umbertoragone/nanoupdi/images/nanoupdi_8.jpg

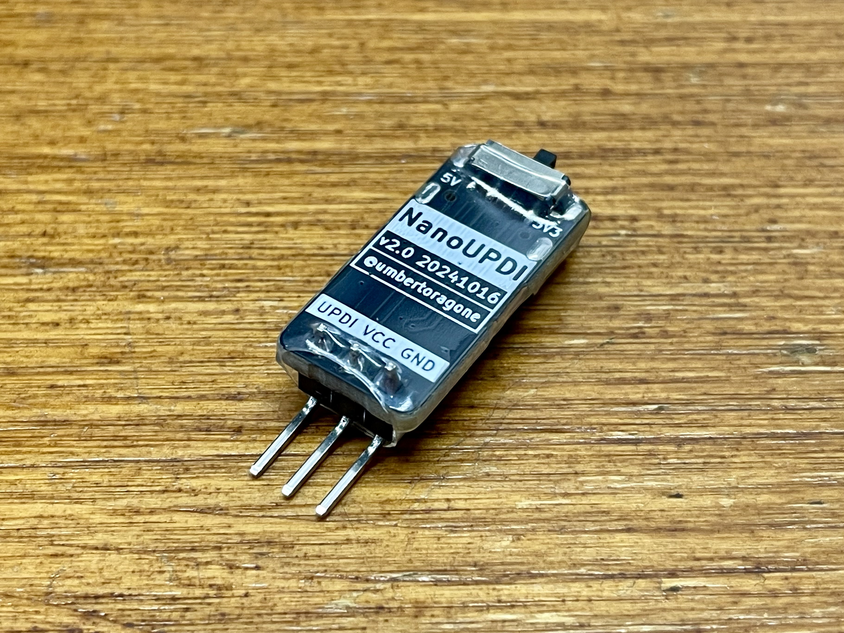
images/nanoupdi_8.jpg
