umbertoragone/nanoupdi/renders/NanoUPDI_programmer_v2_front.jpg

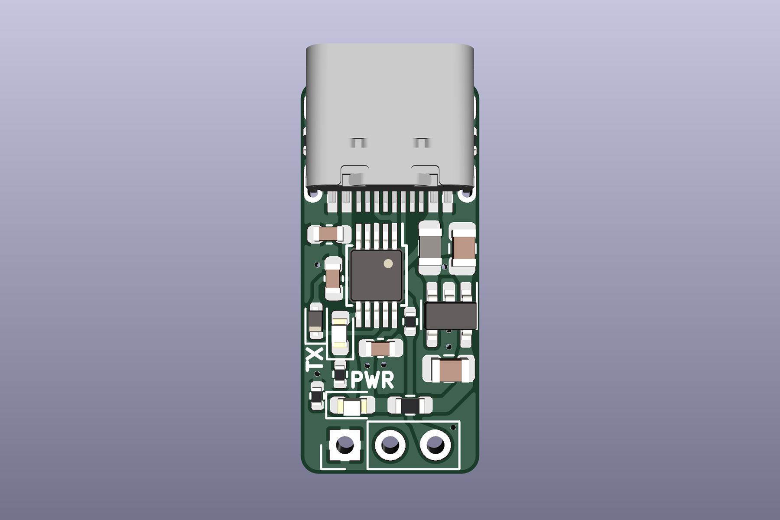
renders/NanoUPDI_programmer_v2_front.jpg
