umbertoragone/nanoupdi/bom/ibom_preview_back.png

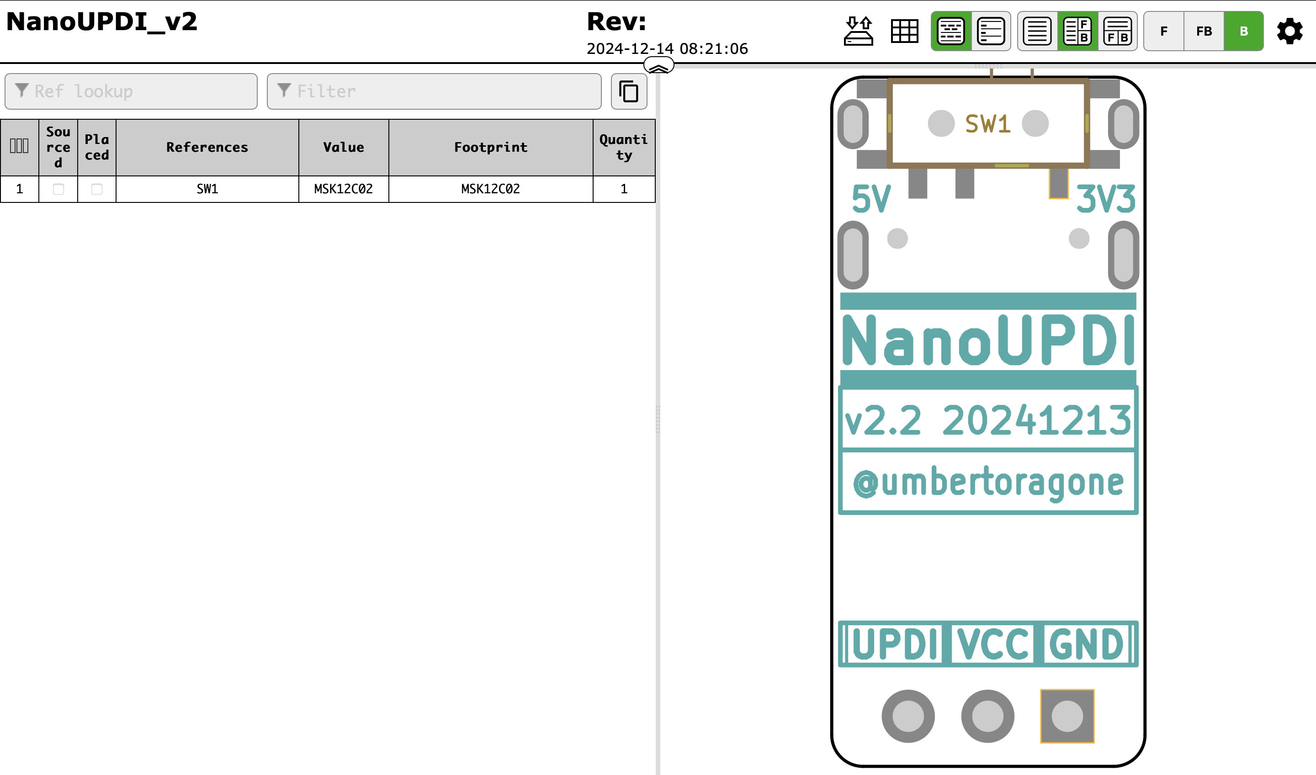
bom/ibom_preview_back.png
