umbertoragone/nanoupdi/bom/ibom_preview_front.png

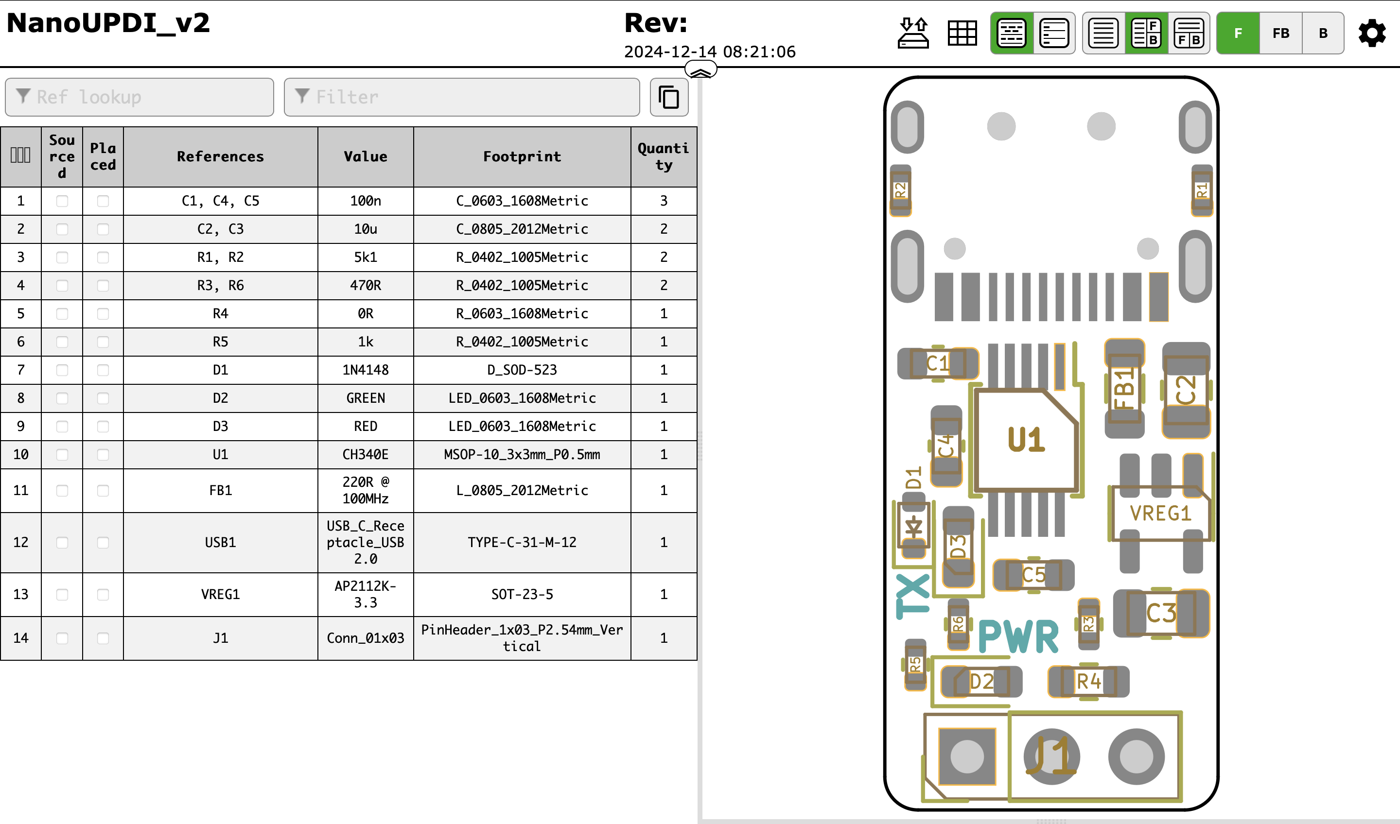
bom/ibom_preview_front.png
